codiak6335/Rabbit-lilygo-T-Pico2350/firmware/rp2350/src/uart_workout_link.cpp

#include "rabbit/rp2350/uart_workout_link.hpp"

#include "hardware/uart.h"

namespace rabbit::rp2350 {
namespace {
constexpr std::size_t kMaxRxBytesPerPoll = 64;
constexpr std::size_t kMaxTxBytesPerPoll = 64;
}

void UartWorkoutLink::poll(protocol::WorkoutService& service, protocol::AudioService& audio, const core::Microseconds now_us) {
    std::size_t received = 0;
    while (uart_is_readable(uart0) && received < kMaxRxBytesPerPoll) {
        protocol::Frame request{};
        protocol::Frame response{};
        protocol::DecodeError error{};
        const auto byte = static_cast<std::uint8_t>(uart_getc(uart0));
        ++received;
        ++stats_.received_bytes;
        if (decoder_.push(byte, request, error)) {
            ++stats_.received_frames;
            if (!audio.handle(request, service.active_session(), service.snapshot(now_us).running, response)) {
                if (request.type == protocol::MessageType::Start && request.session_id == service.active_session() && audio.blocks_start()) {
                    response = {};
                    response.type = protocol::MessageType::Reject;
                    response.session_id = request.session_id;
                    response.request_id = request.request_id;
                    response.payload[0] = static_cast<std::uint8_t>(request.type);
                    response.payload[1] = static_cast<std::uint8_t>(protocol::ServiceError::Command);
                    response.payload_size = 2;
                } else {
                    static_cast<void>(service.handle(request, now_us, response));
                }
            }
            queue(response);
        }
    }
    flush();
}

void UartWorkoutLink::queue(const protocol::Frame& frame) {
    protocol::EncodedFrame encoded{};
    if (!protocol::encode(frame, encoded)) return;
    pending_ = encoded;
    pending_offset_ = 0;
    pending_valid_ = true;
}

void UartWorkoutLink::flush() {
    if (!pending_valid_) return;
    std::size_t sent = 0;
    while (uart_is_writable(uart0) && pending_offset_ < pending_.size && sent < kMaxTxBytesPerPoll) {
        uart_putc_raw(uart0, pending_.bytes[pending_offset_]);
        ++pending_offset_;
        ++sent;
        ++stats_.transmitted_bytes;
    }
    if (pending_offset_ == pending_.size) {
        pending_valid_ = false;
        ++stats_.transmitted_frames;
    }
}

}  // namespace rabbit::rp2350
