codiak6335/Rabbit-lilygo-T-Pico2350/firmware/esp32/main/web_ui.hpp

#pragma once

#include "esp_http_server.h"

namespace rabbit::esp32 {

// Registers the checked-in Coach On Deck UI and bounded local configuration API.
bool register_web_ui(httpd_handle_t server);

}  // namespace rabbit::esp32
